gisellegk/starfield/stellarium-sc/2.5+.png

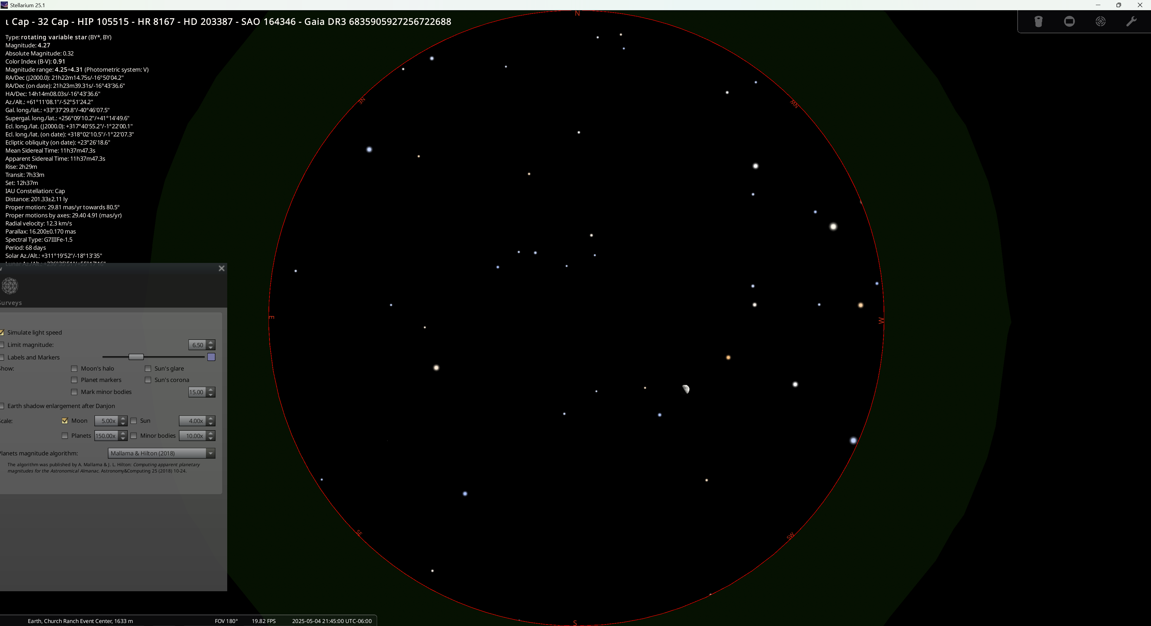
stellarium-sc/2.5+.png
